NUSGreyhats/greybadge25/firmware/ecp5/main/src/challs/fastsecurememory.v

// Code your design here
module fast_regular_synchronous_memory(input clk, input [4:0] address, output reg [7:0] value);
	// memory retrieval
	always @ (posedge clk) begin
		value <= (
			address == 5'd0 ? "f" :
			address == 5'd1 ? "u" :
			address == 5'd2 ? "n" :
			address == 5'd3 ? "{" :
			address == 5'd4 ? "s" :
			address == 5'd5 ? "p" :
			address == 5'd6 ? "e" :
			address == 5'd7 ? "e" :
			address == 5'd8 ? "d" :
			address == 5'd9 ? "s" :
			address == 5'd10 ? "t" :
			address == 5'd11 ? "e" :
			address == 5'd12 ? "r" :
			address == 5'd13 ? "r" :
			address == 5'd14 ? "}" :
			address == 5'd31 ? "L" :
			0
		);
	end
endmodule

// I need to make it secure oh shit
module fast_secure_memory(input clk, input [4:0] address, output [7:0] value);
	wire [4:0] mem_address;
	wire [7:0] mem_value;
	fast_regular_synchronous_memory mem (clk, mem_address, mem_value);

	// Haha its secure now
	assign mem_address = address;
    assign value = ( mem_address == 5'd31 ? mem_value : "?" );
endmodule
