NUSGreyhats/greybadge25/firmware/ecp5/tests/fpgaing/shooting/test.v

module top(input clk, input [4:0] btn, output [7:0] led);
    reg [7:0] shooting = 8'b101;
    reg [31:0] counter;
    always @ (posedge clk) begin
        counter <= counter + 1;
        if (counter == 32_000_00/20) begin
            shooting <= shooting << 1 | shooting[7];
            counter <= 0;
        end
    end

    assign led = ~btn[0] ? btn : shooting;
endmodule
